jfedor2/meet-mute-button/code/src/our_descriptor.h

#ifndef _OUR_DESCRIPTOR_H_
#define _OUR_DESCRIPTOR_H_

#include <stdint.h>

#define REPORT_ID 1

extern const uint8_t our_report_descriptor[];
extern const uint32_t our_report_descriptor_length;

#endif
